erdnaxe/kraby/docs/img/hexapod_devinci.jpg

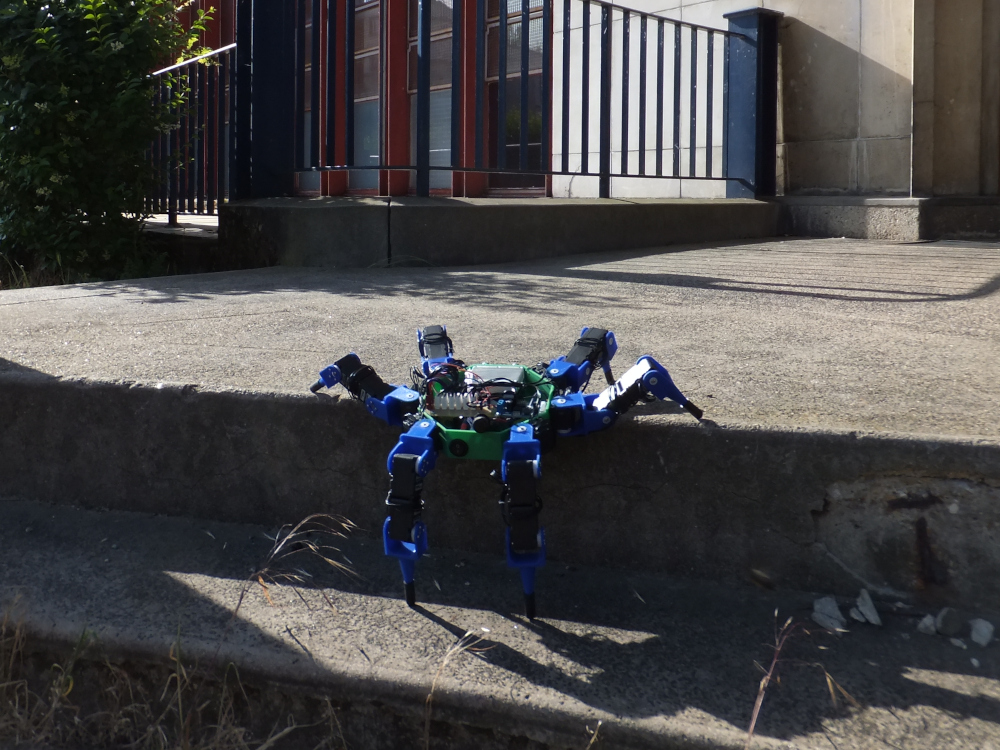
docs/img/hexapod_devinci.jpg
