erdnaxe/kraby/docs/img/onde_leg_env_delta05.png

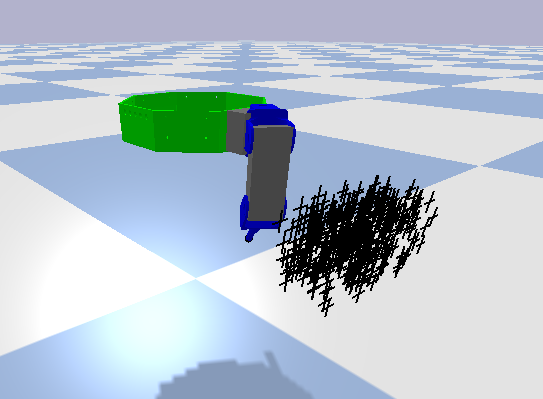
docs/img/onde_leg_env_delta05.png
