erdnaxe/kraby/docs/img/one_leg_env.png

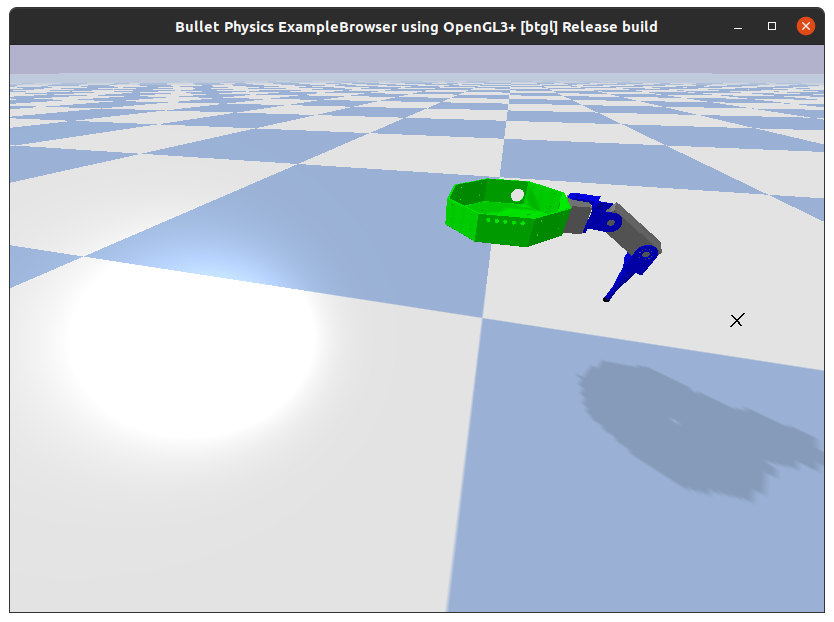
docs/img/one_leg_env.png
