erdnaxe/kraby/printed_circuit_boards/power_board/power_board_bottom.png

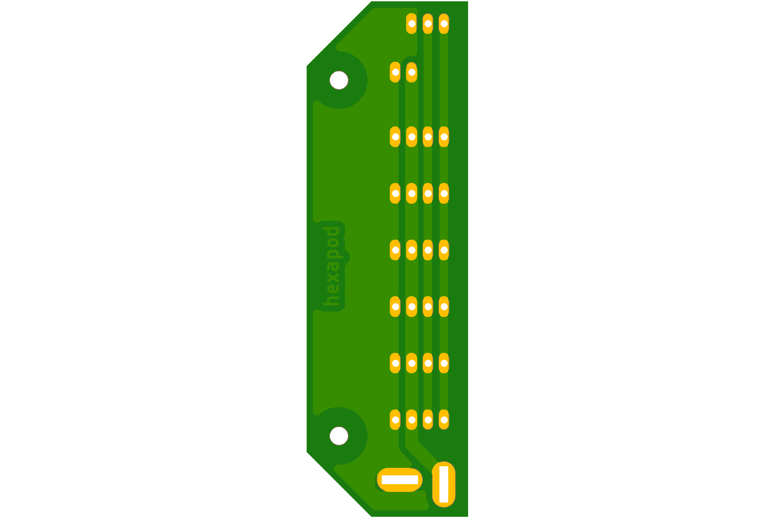
printed_circuit_boards/power_board/power_board_bottom.png
